jwise/x1-expander/x1p-001/dll_mh1_25_4r.png

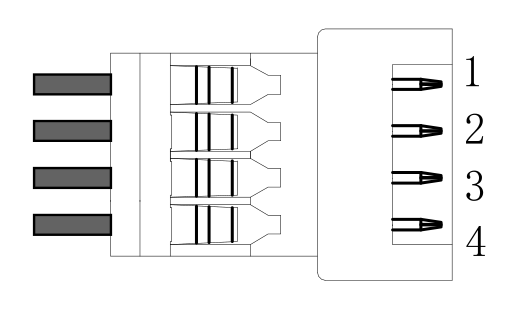
x1p-001/dll_mh1_25_4r.png
